cracked-machine/MidiLedController_hw/RevC/simulation/LEDStatus.asc

GREEN: LED
Q1: npn; 2N3904
R1: res; 1K
R2: res; 1K
R3: res; 1K
R4: res; 4.7K
R5: res; 1K
RED: LED
V1: voltage; 5V
V2: voltage; 0V
Named nets: 5V, 0, SIG, GREENLED, REDLED
.tran 1
